fablabneuch/Pleco/Documentation/Publications/Pompage Pleco_description_annexes.pdf

# Annexes Pompes Pleco

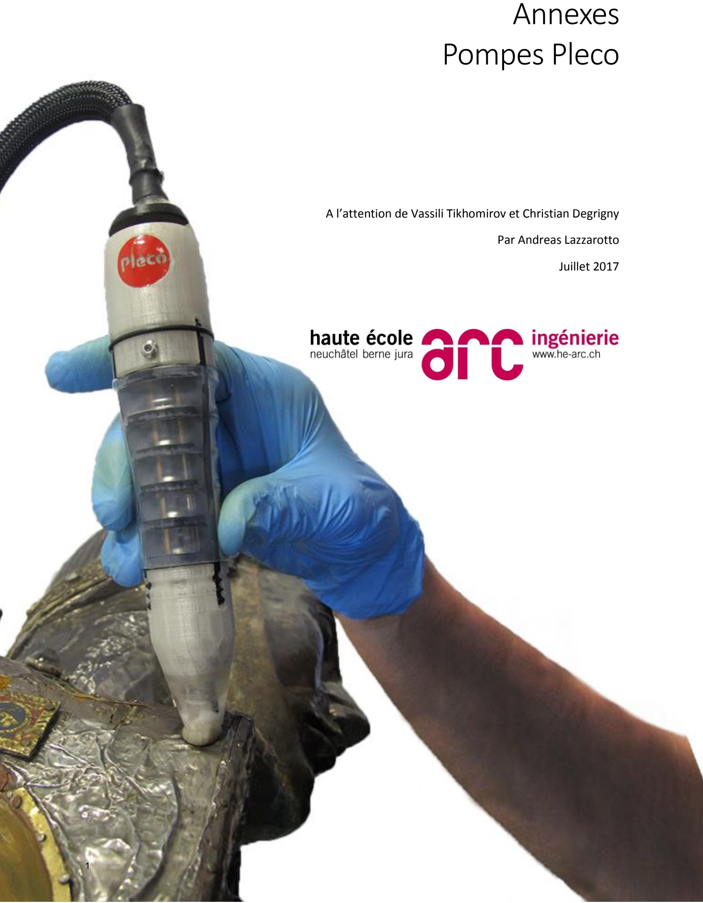
[picture p57: page 1]

A l’attention de Vassili Tikhomirov et Christian Degrigny

Par Andreas Lazzarotto

Juillet 2017

### Table des matières

A1 : Cahier des charges officiel bachelor 2016 | p3
A2 : Analyse fonctionnelle par la méthode APTE | p9
A3 : Table morphologique pompes | p14
B1.1 : Licence CERN EN | p15
B1.2 : Licence CERN traduite en FR | p19
B2 : Datasheet Arduino Leonardo | p22
B3 : Datasheet Pololu A4988 | p27

Annexe A1 : cahier des charges officiel bachelor 2016

Projet P3 & Bachelor 2015-2016 | 16IDE-TB531

# Pompes pour Pleco

Etudiant : | Lazzarotto-Pinösch Andreas | andreas.lazzarotto- pinosch@he-arc.ch
Mandant : | He-arc Conservation-Restauration
Personnes de contact : | Degrigny Christian | Christian.Degrigny@he-arc.ch
Confidentialité : | Non
Responsable du Projet : | Tikhomirov Vassili | Vassili.Tikhomirov@he-arc.ch

Description et contexte

Dans le cadre du projet P3, il m’est demandé de poursuivre mon travail commencé en cours d’anthropotechnologie de deuxième année d’ingénierie à la HE-ARC de Neuchâtel.
Le projet consiste à remplacer les pompes actuelles du pinceau électrolytique Pleco par une alternative open source / open hardware.

Objectifs
Concevoir deux pompes pour le pinceau électrolytique Pleco en tenant compte de différentes contraintes liées à l’environnement de production, à la philosophie open source et à la conception orientée vers l’utilisateur.

### 2. Conditions requises

### 2.1 Conditions relationnelles

- Une séance hebdomadaire doit être planifiée avec le responsable du projet.
- Différentes étapes doivent être validées avec le mandant, telles que la planification, le concept, la construction, les analyses. Des revues de projet doivent donc avoir lieu régulièrement avec ce dernier.
- Un journal de travail doit être tenu par le candidat au diplôme.
- Chaque semaine, un bilan succinct sur l'avancement doit être fait et les objectifs de la semaine à venir doivent être fixés. Ce document doit être transmis aux différents acteurs du projet.

### 2.2 Conditions techniques

- Le rapport de débit entre les deux pompes doit être de 1 à 10
- Moyen de comparaison entre les débits
- Faire circuler de l’air
- Avoir une fonction amorçage (bouton mettant débit max)
- Avoir une fonction pause
- Etre le plus silencieuses possible
- Supporter des pH compris entre 4 et 10.5
- Les pièces doivent pouvoir être produites dans un Fablab
- Le projet est produit dans le cadre d’une licence Open Source / Open hardware
- Ergonomie adaptée aux conservateurs restaurateurs
- Coût le plus faible possible

### 3. Travaux à exécuter

- Rapport de projet, méthodologie et conception.
- Prototypes fonctionnels

### 4. Organisation du projet P3

### 4.1 Planification

- | Début du projet P3 | 15 Février 2016
- | Liste des tâches et planification initiale à remettre | Selon professeur
- | Présentation orale et rendu de l’auto-évaluation | 13 mai 2016. Semaine 19 la date
| | sera précisée ultérieurement :

### 4.2 Présentation et expertise

- A la fin du projet P3, une présentation de 10 minutes maximum devra être faite devant le collège de professeurs. Celle-ci sera suivie de 5 minutes de questions du groupe de
| professeur(e)s.
- Chaque étudiant remettra sa grille d’auto-évaluation.

### 4.3 Annexes

- Descriptif du module Projet P3 : ING-DM3580-14

### 5. Organisation du projet Bachelor

### 5.1 Planification

- | Début du projet Bachelor | 23 mai 2016
- | Travail, rapport à remettre | 15 Juillet, au plus tard à 16h30
- Poster
- Présentation orale du projet
| | pour l'expertise du travail de diplôme
| | Semaine du 22 au 26 août, la date
| | sera précisée ultérieurement
- | Expertise du travail de Bachelor | Semaine 22 au 26 août, la date sera
| | précisée ultérieurement

### 5.2 Présentation et expertise

- L'étude et le rapport de Bachelor doivent être remis en trois exemplaires papier et un
| exemplaire sur support informatique.
- Une affiche de présentation du projet Bachelor au format A4 doit être réalisée avec approbation
| du mandant.
- Lors de l’expertise du travail de Bachelor,
- Une présentation orale de 15 minutes devra être faite devant le collège de professeurs
| garant de l’équité de jugement entre les TB.
- Une note de présentation est attribuée par le collège de professeurs.
- La soutenance se déroule ensuite avec le professeur responsable, l’expert et le
| mandant s’il le souhaite.
- A la suite de la soutenance, 3 notes sont attribuées : sur le déroulement du projet, le rapport et l’expertise. Si l’écart entre les notes du professeur et de l’expert est supérieur à 1 de manière irréconciliable, le TB fera l’objet d’une nouvelle expertise avec un autre expert et autre professeur de l’orientation.
- La note d’expertise est la moyenne pondérée des notes de présentation et de
| soutenance.

### 5.3 Annexes

- Description du module Travail de Bachelor : ING-DM3985-14
- Feuille d’enregistrement du travail de Bachelor ING-FOR3-MOD001
- Contrat Ecole – Entreprise pour projet d’étudiant ING-FOR3-MOD002
- Contrat de propriété intellectuelle et confidentialité ING-FOR3-MOD004
- Rédaction de l’affiche du travail de Bachelor : ING-FOR3-MOD005

### 6. Signatures

Neuchâtel, le 26 février 2016

L’étudiant : | Le responsable du travail de diplôme :
Lazzarotto-Pinösch Andreas | Tikhomirov Vassili
Le mandant : | La responsable de filière :
Degrigny Christian | Briquez Valérie

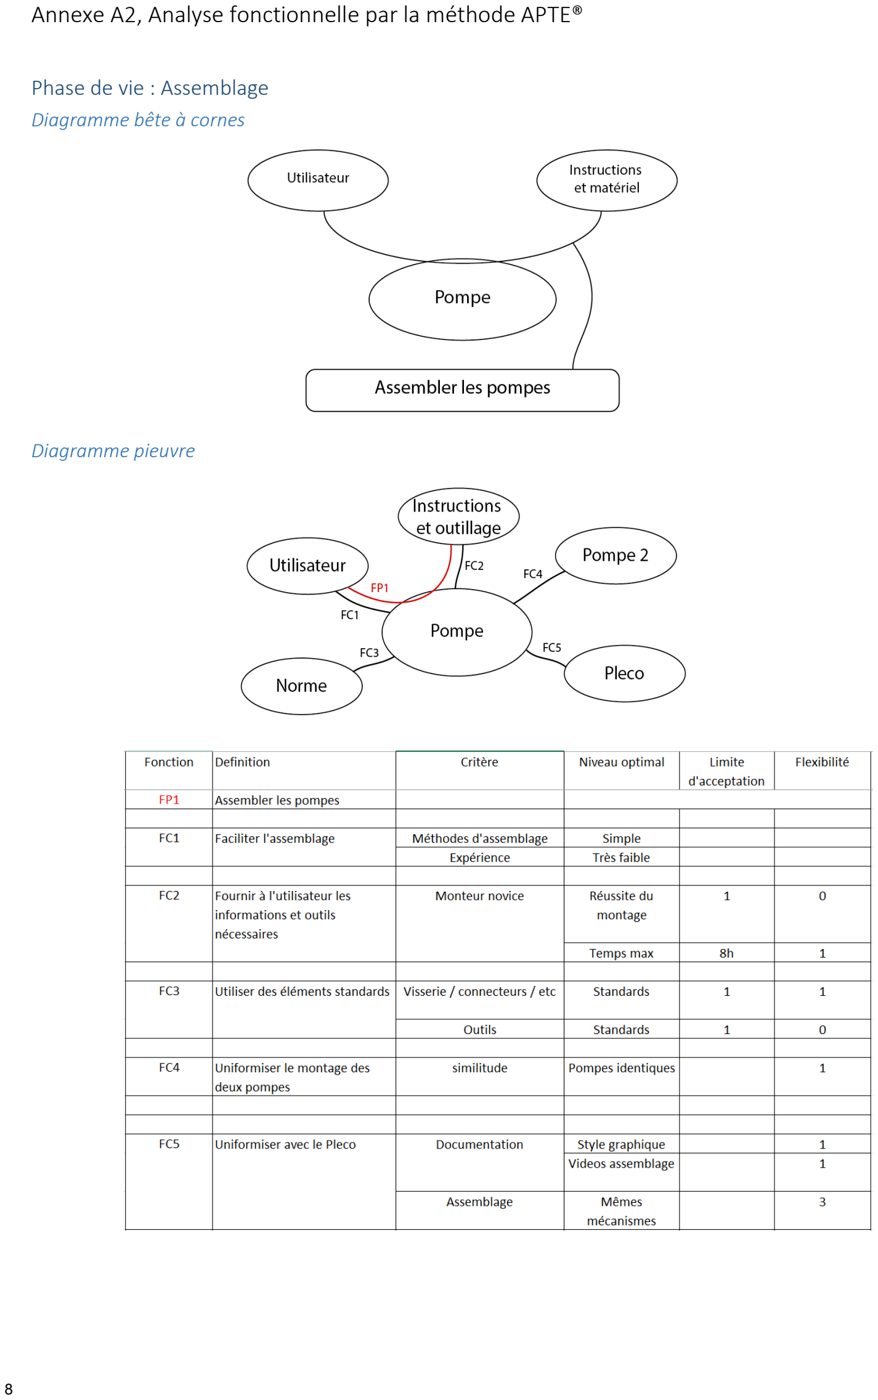
[picture p58: page 9]

### Annexe A2, Analyse fonctionnelle par la méthode APTE®

Phase de vie : Assemblage
Diagramme bête à cornes

Diagramme pieuvre

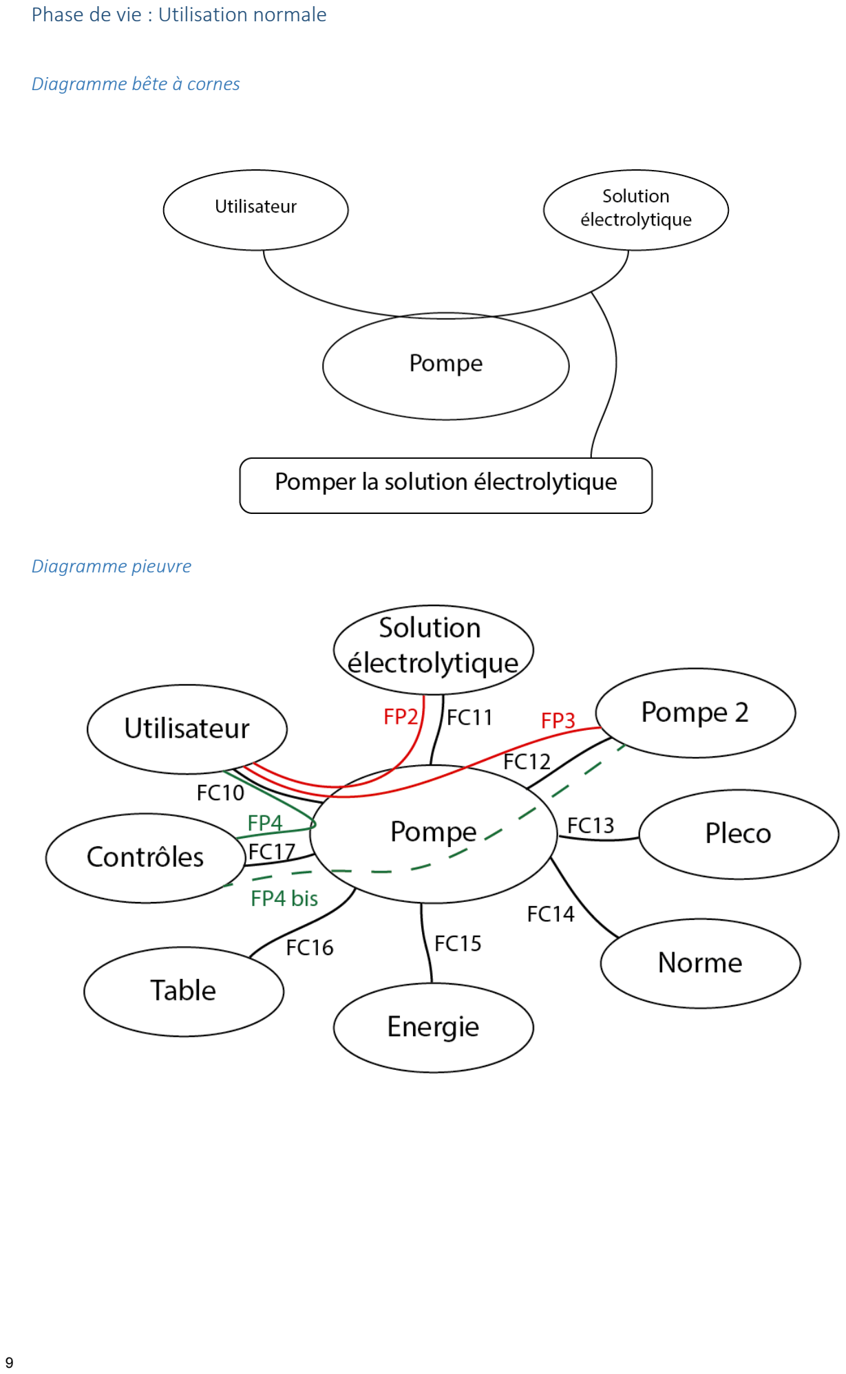
[picture p59: page 10]

Phase de vie : Utilisation normale

Diagramme bête à cornes

Diagramme pieuvre

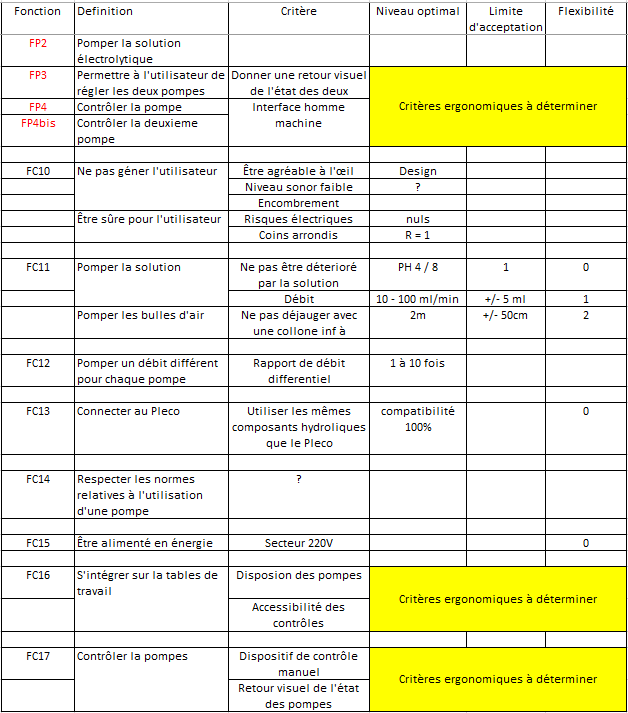
[picture p60: figure]
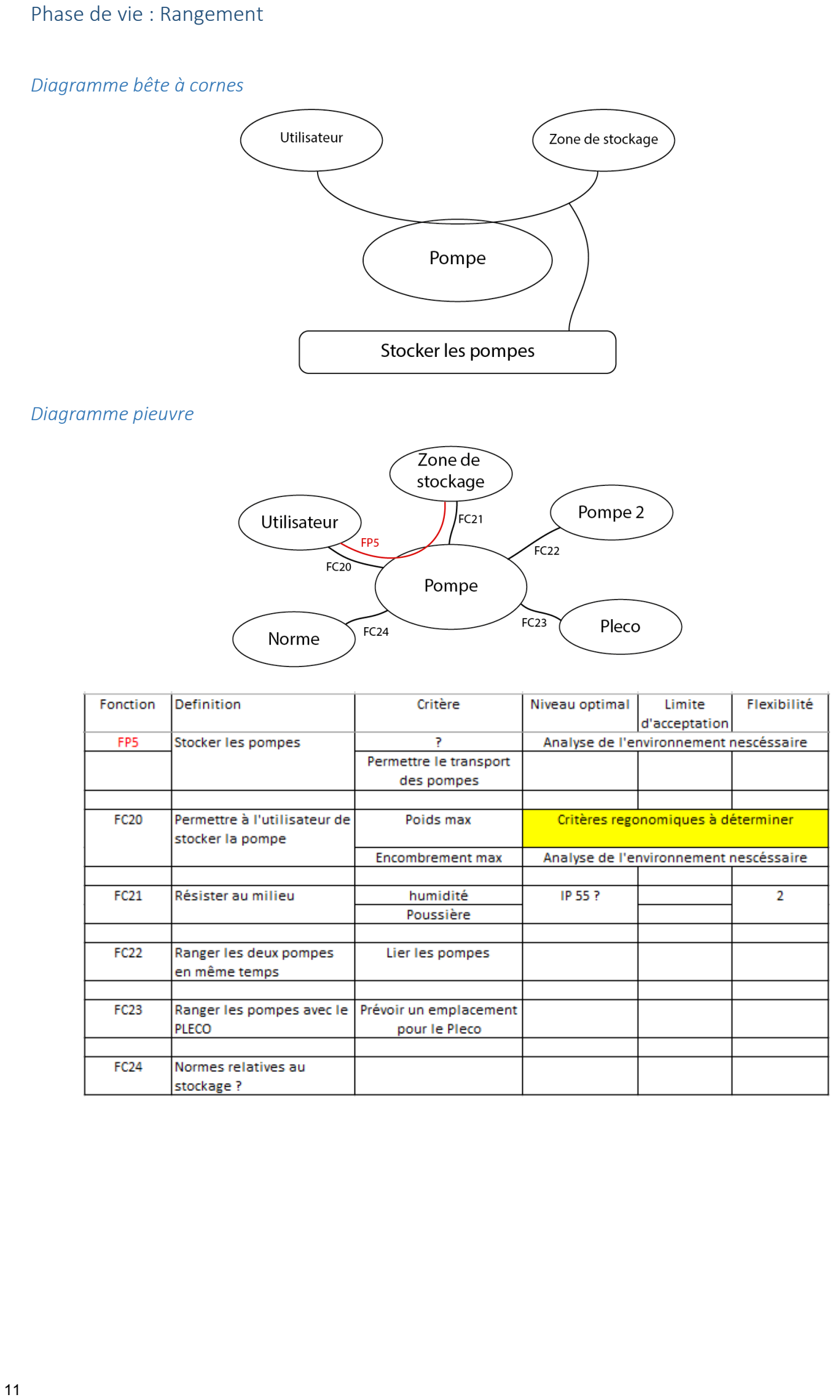
[picture p61: page 12]

Phase de vie : Rangement

Diagramme bête à cornes

Diagramme pieuvre

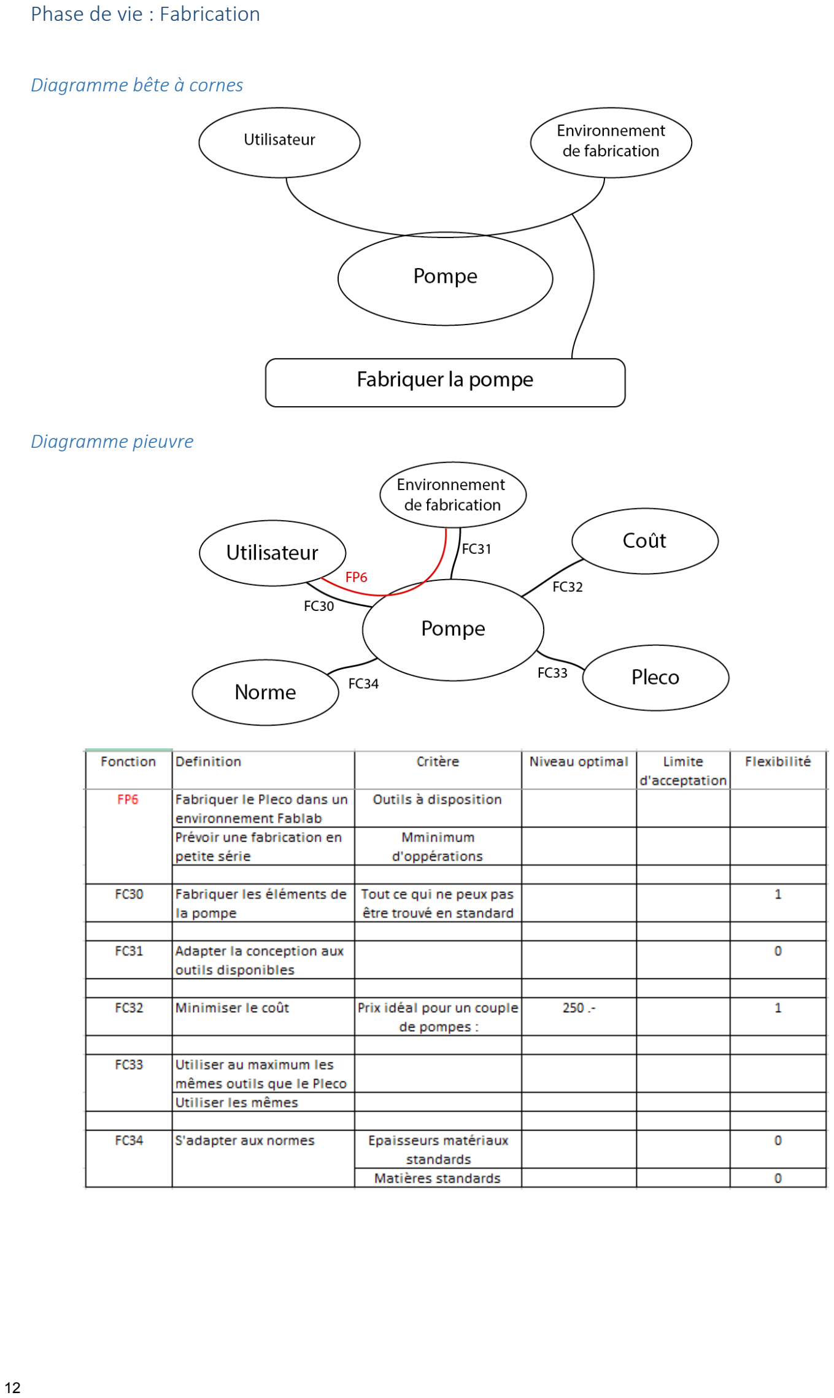
[picture p62: page 13]

Phase de vie : Fabrication

Diagramme bête à cornes

Diagramme pieuvre

Type rotative axiale rotative centrifuge à pistons pompe à palettes peristaltique à engrenages à membranes

illustration

principe physique Hélice de bateau utilisation de la force centrifuge Meme principe qu'un moteur

Le palletes restent plaquées contre
le carter et le changement de

volume entre celle-ci créent une

dépression

On comprime un tube souble

locallement pour pousser le fluide

qu'il contient

Le liquide passe a l'extérieur des

roues en étant prisonier entre les

dentures

un mouvement d'allé retour d'une
membrane dans une chambre,

assosié à des valve anti-retour met
le fluide en mouvement

Stabilitée du débit Débit constant Débit constant débit pulsé Débit constant pulsé constant pulsé

Résistance chimique Tous les éléments en contacts

doivent résister

Tous les éléments en contacts

doivent résister

Tous les éléments en contacts

doivent résister

Tous les éléments en contacts

doivent résister

Seul le tuyau est en contact avec le

fluide

Tous les éléments en contacts

doivent résister

possibilité d'utiliser des

membranes résistantes

chimiquement ( PTFE / AL / etc)

Type d'étanchéitée étanchéité par garniture sur un

arbre

étanchéité par garniture sur un

## arbre ajustement piston/carter fermeture de carter / ajustement

## hub/ pallettes/carter Pas d''étanchéitée fermeture de carter / ajustement

carter / engrenage membrane / fermeture de carter

Précision de la fabrication Critique tolérante Critique Critique Très tolérante Critique Tolérante

Fabrication dans un Fablab Dificille Difficile Très difficile Difficile Facile Difficile Moyennement dificile

## Annexe A3 : Table morphologique pompes

Annexe B1.1 Licence CERN EN

CERN Open Hardware Licence v1.2

Preamble

Through this CERN Open Hardware Licence ("CERN OHL") version 1.2, CERN wishes to provide a tool to foster collaboration and sharing among hardware designers. The CERN OHL is copyright CERN. Anyone is welcome to use the CERN OHL, in unmodified form only, for the distribution of their own Open Hardware designs. Any other right is reserved. Release of hardware designs under the CERN OHL does not constitute an endorsement of the licensor or its designs nor does it imply any involvement by CERN in the development of such designs.

1. Definitions

In this Licence, the following terms have the following meanings:

“Licence” means this CERN OHL.

“Documentation” means schematic diagrams, designs, circuit or circuit board layouts, mechanical drawings, flow charts and descriptive text, and other explanatory material that is explicitly stated as being made available under the conditions of this Licence. The Documentation may be in any medium, including but not limited to computer files and representations on paper, film, or any other media.

“Documentation Location” means a location where the Licensor has placed Documentation, and which he believes will be publicly accessible for at least three years from the first communication to the public or distribution of Documentation.

“Product” means either an entire, or any part of a, device built using the Documentation or the modified Documentation.

“Licensee” means any natural or legal person exercising rights under this Licence.

“Licensor” means any natural or legal person that creates or modifies Documentation and subsequently communicates to the public and/ or distributes the resulting Documentation under the terms and conditions of this Licence.

A Licensee may at the same time be a Licensor, and vice versa.

Use of the masculine gender includes the feminine and neuter genders and is employed solely to facilitate reading.

2. Applicability
2.1. This Licence governs the use, copying, modification, communication to the public and distribution of the Documentation, and the manufacture and distribution of Products. By exercising any right granted under this Licence, the Licensee irrevocably accepts these terms and conditions.
2.2. This Licence is granted by the Licensor directly to the Licensee, and shall apply worldwide and without limitation in time. The Licensee may assign his licence rights or grant sub-licences.
2.3. This Licence does not extend to software, firmware, or code loaded into programmable devices which may be used in conjunction with the Documentation, the modified Documentation or with Products, unless such software, firmware, or code is explicitly expressed to be subject to this Licence. The use of such software, firmware, or code is otherwise subject to the applicable licence terms and conditions.
3. Copying, modification, communication to the public and distribution of the Documentation
3.1. The Licensee shall keep intact all copyright and trademarks notices, all notices referring to Documentation Location, and all notices that refer to this Licence and to the disclaimer of warranties that are included in the Documentation. He shall include a copy thereof in every copy of the Documentation or, as the case may be, modified Documentation, that he communicates to the public or distributes.
3.2. The Licensee may copy, communicate to the public and distribute verbatim copies of the Documentation, in any medium, subject to the requirements specified in section 3.1.
3.3. The Licensee may modify the Documentation or any portion thereof provided that upon modification of the Documentation, the Licensee shall make the modified Documentation available from a Documentation Location such that it can be easily located by an original Licensor once the Licensee communicates to the public or distributes the modified Documentation under section 3.4, and, where required by section 4.1, by a recipient of a Product. However, the Licensor shall not assert his rights under the foregoing proviso unless or until a Product is distributed.
3.4. The Licensee may communicate to the public and distribute the modified Documentation (thereby in addition to being a Licensee also becoming a Licensor), always provided that he shall:
a) comply with section 3.1;
b) cause the modified Documentation to carry prominent notices stating that the Licensee has modified the Documentation, with the date and description of the modifications;
c) cause the modified Documentation to carry a new Documentation

Location notice if the original Documentation provided for one;

d) make available the modified Documentation at the same level of abstraction as that of the Documentation, in the preferred format for making modifications to it (e.g. the native format of the CAD tool as applicable), and in the event that format is proprietary, in a format viewable with a tool licensed under an OSI-approved license if the proprietary tool can create it; and
e) license the modified Documentation under the terms and conditions of this Licence or, where applicable, a later version of this Licence as may be issued by CERN.
3.5. The Licence includes a non-exclusive licence to those patents or registered designs that are held by, under the control of, or sub-licensable by the Licensor, to the extent necessary to make use of the rights granted under this Licence. The scope of this section 3.5 shall be strictly limited to the parts of the Documentation or modified Documentation created by the Licensor.
4. Manufacture and distribution of Products
4.1. The Licensee may manufacture or distribute Products always provided that, where such manufacture or distribution requires a licence under this Licence the Licensee provides to each recipient of such Products an easy means of accessing a copy of the Documentation or modified Documentation, as applicable, as set out in section 3.
4.2. The Licensee is invited to inform any Licensor who has indicated his wish to receive this information about the type, quantity and dates of production of Products the Licensee has (had) manufactured
5. Warranty and liability
5.1. DISCLAIMER – The Documentation and any modified Documentation are provided "as is" and any express or implied warranties, including, but not limited to, implied warranties of merchantability, of satisfactory quality, non-infringement of third party rights, and fitness for a particular purpose or use are disclaimed in respect of the Documentation, the modified Documentation or any Product. The Licensor makes no representation that the Documentation, modified Documentation, or any Product, does or will not infringe any patent, copyright, trade secret or other proprietary right. The entire risk as to the use, quality, and performance of a Product shall be with the Licensee and not the Licensor. This disclaimer of warranty is an essential part of this Licence and a condition for the grant of any rights granted under this Licence. The Licensee warrants that it does not act in a consumer capacity.
5.2. LIMITATION OF LIABILITY – The Licensor shall have no liability for direct, indirect, special, incidental, consequential, exemplary, punitive or other damages of any character including, without limitation, procurement of substitute goods or services, loss of use, data or profits, or business interruption, however caused and on any theory of contract, warranty, tort (including negligence), product liability or otherwise, arising in any way in relation to the Documentation, modified Documentation and/or the use, manufacture or distribution of a Product, even if advised of the possibility of such damages, and the Licensee shall hold the Licensor(s) free and harmless from any liability, costs, damages, fees and expenses, including claims by third parties, in relation to such use.
6. General
6.1. Except for the rights explicitly granted hereunder, this Licence does not imply or represent any transfer or assignment of intellectual property rights to the Licensee.
6.2. The Licensee shall not use or make reference to any of the names (including acronyms and abbreviations), images, or logos under which the Licensor is known, save in so far as required to comply with section 3. Any such permitted use or reference shall be factual and shall in no event suggest any kind of endorsement by the Licensor or its personnel of the modified Documentation or any Product, or any kind of implication by the Licensor or its personnel in the preparation of the modified Documentation or Product.
6.3. CERN may publish updated versions of this Licence which retain the same general provisions as this version, but differ in detail so far this is required and reasonable. New versions will be published with a unique version number.
6.4. This Licence shall terminate with immediate effect, upon written notice and without involvement of a court if the Licensee fails to comply with any of its terms and conditions, or if the Licensee initiates legal action against Licensor in relation to this Licence. Section 5 shall continue to apply.

Annexe B1.2 Licence CERN traduite en FR

Licence CERN Matériel Ouvert v1.2

PRÉAMBULE
Au travers cette Licence CERN Matériel Ouvert ("CERN OHL") en version 1.2, le CERN espère fournir un outil permettant de favoriser la collaboration et le partage parmi les concepteurs de Matériels. Le CERN est détenteur des droits d'auteur sur la CERN OHL. Tout le monde est le bienvenu à utiliser la CERN OHL, uniquement dans sa forme non modifiée, pour la distribution de ses conceptions de Matériel Ouvert.
Tout autre droit est réservé. La publication de conceptions de matériel sous CERN OHL ne constitue pas une acceptation du concédant ou de ses conceptions, ni n'implique une quelconque participation du CERN dans le développement de telles conceptions.
1. DÉFINITIONS
Dans cette Licence, les termes suivants ont les significations suivantes:
"Licence" signifie cette CERN OHL.
"Documentation" signifie les diagrammes schématiques, les plans, les tracés de circuit ou de circuit imprimé, les logigrammes et tout texte descriptif, et tout autre information qui est explicitement mentionné comme étant disponible sous les conditions de cette licence. La Documentation peut exister sous n'importe quel support, incluant mais ne se limitant pas aux fichiers informatiques et aux représentations sur papier, film, ou sur tout autre support. "Emplacement de la Documentation" signifie un emplacement où le Concédant a placé la Documentation, et qui sera, espère le Concédant, publiquement accessible au moins pour les trois années qui suivent la première communication au public, ou la première distribution, de la Documentation.
"Produit" signifie aussi bien tout ou partie d'un dispositif construit en utilisant la
Documentation ou la Documentation Modifiée.
"Concessionnaire" signifie toute personne physique ou morale qui exerce des droits couverts par cette Licence.
"Concédant" signifie toute personne physique ou morale qui créée ou modifie la Documentation et qui subséquemment communique au public et/ou distribue la Documentation qui en résulte sous les termes et conditions de cette Licence.
Un Concédant peut être à la fois un Concessionnaire, et vice versa.
L'utilisation du genre masculin inclus le genre féminin et le genre neutre, et est employé uniquement pour faciliter la lecture.
2. APPLICABILITÉ
2.1 Cette licence régit l'utilisation, la reproduction, la modification, la communication au public et la distribution de la Documentation, ainsi que la fabrication et distribution des Produits. Par l'exercice de tout droit accordé en vertu de cette Licence, le Concessionnaire accepte de façon irrévocable ces termes et conditions.
2.2 Cette Licence est accordée par le Concédant directement au
Concessionnaire, et elle s'applique dans le monde entier et sans limitation dans le temps. Le Concessionnaire peut céder ses droits de licence ou concéder des sous-licences.
2.3 Cette licence ne s'étend pas aux logiciels, aux micrologiciels, ou aux codes chargés dans des dispositifs programmables qui peuvent être utilisés en conjonction avec la Documentation, la Documentation modifiée ou avec les Produits, à moins qu'un tel logiciel, micrologiciel, ou code ne soit explicitement exprimé comme étant soumis à cette Licence. Autrement, l'utilisation d'un tel logiciel, micrologiciel, ou code est, soumis aux termes et conditions de la licence applicable.
3. REPRODUCTION, MODIFICATION, COMMUNICATION AU PUBLIC
ET DISTRIBUTION DE LA DOCUMENTATION.
3.1 Le Concessionnaire doit conserver intacts tous les droits d'auteurs et les licences de marques, toutes les notices se référant à l'Emplacement de laDocumentation, et toutes les notices qui se réfèrent à cette Licence et à la déclaration d'absence de garanties qui sont inclus dans la Documentation.

3.2 Le Concessionnaire peut copier, communiquer au public et distribuer des copies verbatim de la Documentation, sur n'importe quel support, selon les exigences spécifiées dans la section 3.1.
3.3 Le Concessionnaire peut modifier la documentation ou toute portion de celle-ci à condition que lors de la modification de la documentation, le Concessionnaire rende la Documentation Modifiée disponible depuis un Emplacement de la Documentation de telle sorte à ce qu'elle soit facilement localisée par un Concédant initial dès que le concessionnaire communique au public ou distribue la Documentation Modifiée en vertu de la section 3.4, et, comme stipulé par la section 4.1, par un destinataire d'un Produit. Toutefois, le Concédant ne pourra faire valoir ses droits en vertu de la clause restrictive précédente, à moins que ou jusqu'à ce que, un Produit soit distribué.
3.4 Le Concessionnaire peut communiquer au public et distribuer la Documentation Modifiée (de ce fait en plus d'être un Concessionnaire devenant également un Concédant ), à condition qu'il doive toujours :
a) être conforme avec la section 3.1;
b) faire de telle sorte à ce que la Documentation Modifiée contienne de
façon bien en évidence des notices stipulant que le Concessionnaire a modifié la Documentation, avec la date et la description des modifications;
c) faire de telle sorte à ce que la Documentation Modifiée contienne un nouvel Emplacement de Documentation lorsque la Documentation initiale en prévit un;
d) rendre disponible la Documentation Modifiée dans un même niveau d'abstraction que celui de la Documentation, dans une forme préférée pour faire des modifications sur celle-ci (càd: le format natif d'un outil de CAO qui s'applique), et dans le cas où ce format est propriétaire, dans un format consultable avec un outil régit par des termes et conditions sous une licence approuvée par l'OSI si l'outil propriétaire peut le créer; et e) placer la documentation Modifiée sous les termes et conditions de cette Licence ou, lorsque cela s'applique, une version postérieure de cette Licence susceptible d'être émise par le CERN.
3.5. La Licence inclus une licence non-exclusive pour ces brevets ou ces marques déposées qui sont détenus par, sous le contrôle de, ou souslicenciable par le Concédant, dans la mesure nécessaire pour faire usage des droits accordés en vertu de cette Licence. Le champ de cette section
3.5 doit être strictement limité aux parties de le Documentation ou de la
Documentation Modifiée créée par le Concédant.
4. FABRICATION ET DISTRIBUTION DES PRODUITS
4.1. Le Concessionnaire peut fabriquer ou distribuer les Produits à la condition permanente que, lorsqu'une telle fabrication ou distribution requiert une licence sous cette Licence, le Concessionnaire fournisse à chaque destinataire de telle produits un moyen facile pour accéder à une copie de la Documentation ou de la Documentation Modifiée, comme cela s'applique, comme établit en section 3.
4.2. Le Concessionnaire est invité à informer tout Concédant qui a indiqué qu'il souhaite recevoir cette information à propos du type, de la quantité et des dates de production des produits que le Concessionnaire a (avait) fabriqués.
5. GARANTIE ET RESPONSABILITÉ
5.1 RENONCIATION - La Documentation et la Documentation
Modifiée sont fournies "en l'état" et toute garantie exprimée ou tacite, incluant, mais ne se limitant pas à, les garanties tacites de commercialisation (en terme de qualité, état, qualité, existence), de qualité satisfaisante, non-violation de droits de tiers, et d'adéquation à un objectif particulier ou à un usage, est exclue en ce qui concerne la Documentation, la Documentation modifiée ou tout Produit. Le Concédant ne fait aucune déclaration qui stipulerait que la Documentation, la Documentation Modifiée, ou tout Produit, est ou sera en violation avec un brevet, un droit d'auteur, un secret d'état ou une autre droit de propriété. La totalité du risque quant à l'utilisation, la qualité, et la performance d'un Produit, est assumé par le Concessionnaire et pas par le Concédant. Cette renonciation de garantie est une partie essentielle de cette Licence et une condition pour l'octroie de tous droits en vertu de cette Licence. Le Concessionnaire garantie qu'il n'agit pas en qualité de consommateur.

5.2 LIMITE DE RESPONSABILITÉ - Le Concédant ne peut aucunement être tenu responsable d'aucune façon pour des dommages de tout type directs, indirects, spéciaux, consécutifs, exemplaires, punitifs ou autres, incluant, mais pas limité aux, achats de marchandises de remplacement ou de services, perte d'utilisation, de données ou de profits, ou interruption d'activités, même provoqués et fondés sur une quelconque théorie de contrat, de garantie, de délis (incluant la négligence), de responsabilité liée au produit ou quelque soit d'autre, survenant de n'importe quelle façon en relation avec la Documentation, la Documentation Modifiée et/ou l'utilisation, la fabrication ou la distribution d'un produit, même s'il est avisé de l'éventualité de tels dommages, et il est de la responsabilité du Concessionnaire de tenir le(s) Concédant(s) libre(s) et exonéré(s) toute responsabilité, coûts, dommages, frais et dépenses, y compris les réclamations de tiers, en relation avec à une telle utilisation.
6. GENERAL
6.1 À l'exception des droits explicitement accordés aux présentes, cette licence ni ne signifie ni ne représente un quelconque transfert ou une quelconque cession des droits de propriété intellectuelle au Concessionnaire.
6.2. Le Concessionnaire ne doit pas utiliser ou faire référence à de quelconques noms (incluant les acronymes et les abréviations), images, ou logos en vertu desquels le Concédant est connu, sauf dans la mesure où cela est requis pour se conformer avec la section 3. Une telle utilisation autorisée ou référence doit être factuelle et ne doit en aucun cas suggérer une quelconque sorte d'approbation, par le Concédant ou son personnel, de la Documentation Modifiée ou de tout Produit, ou une quelconque implication par le Concédant ou son personnel, dans la préparation de la Documentation Modifiée ou du Produit.
6.3. Le CERN peut publier des versions mises à jour de cette Licence qui conservent les mêmes dispositions générales que cette version, mais diffèrent dans les détails dans la limite du nécessaire et du raisonnable. Les nouvelles versions seront publiées avec un numéro de version unique.
6.4. Cette Licence prend fin avec effet immédiat, moyennant un préavis écrit et sans intervention d'un tribunal si le Concessionnaire échoue à se mettre en conformité avec un quelconque de ses termes et conditions, ou si le Concessionnaire initie une action en justice contre le Concédant enrelation avec cette Licence. La section 5 doit continuer à s'appliquer.

## Annexe B1 : Datasheet Arduino Leonardo

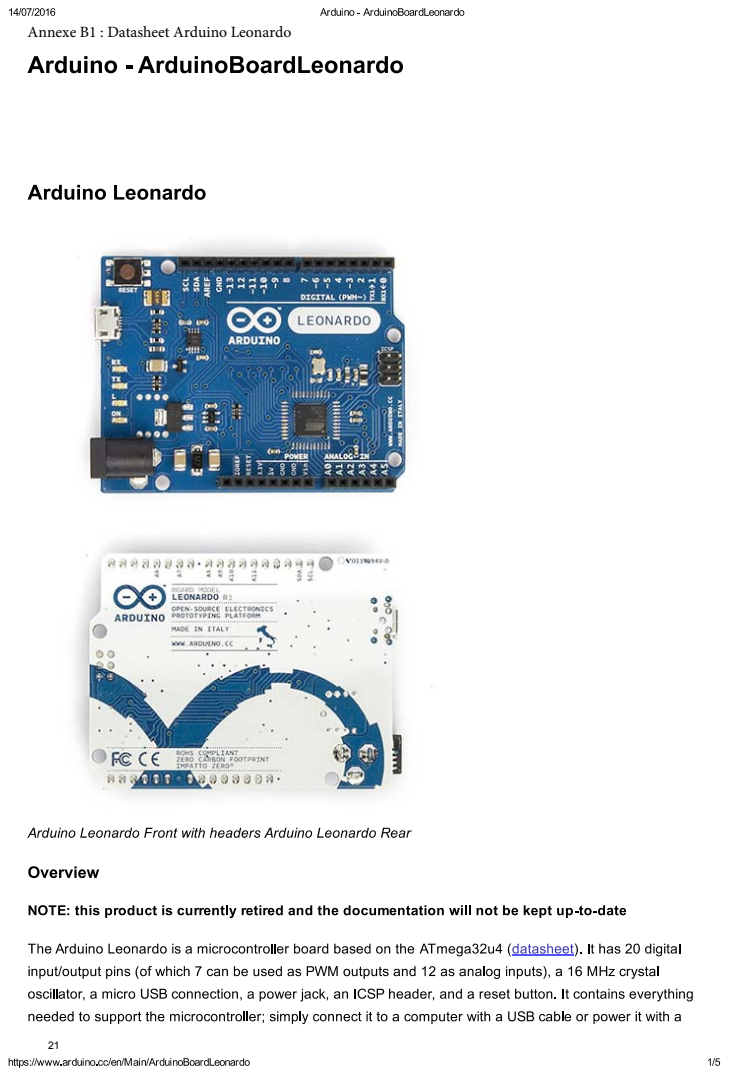
[picture p63: page 22]

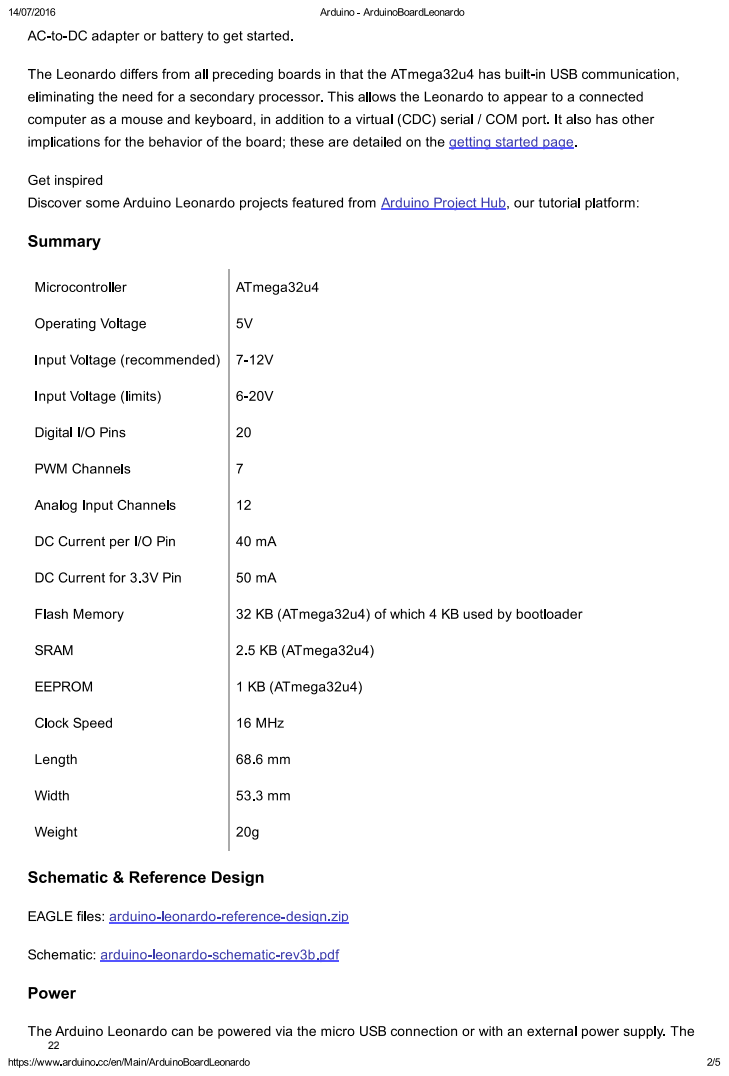
[picture p64: page 23]

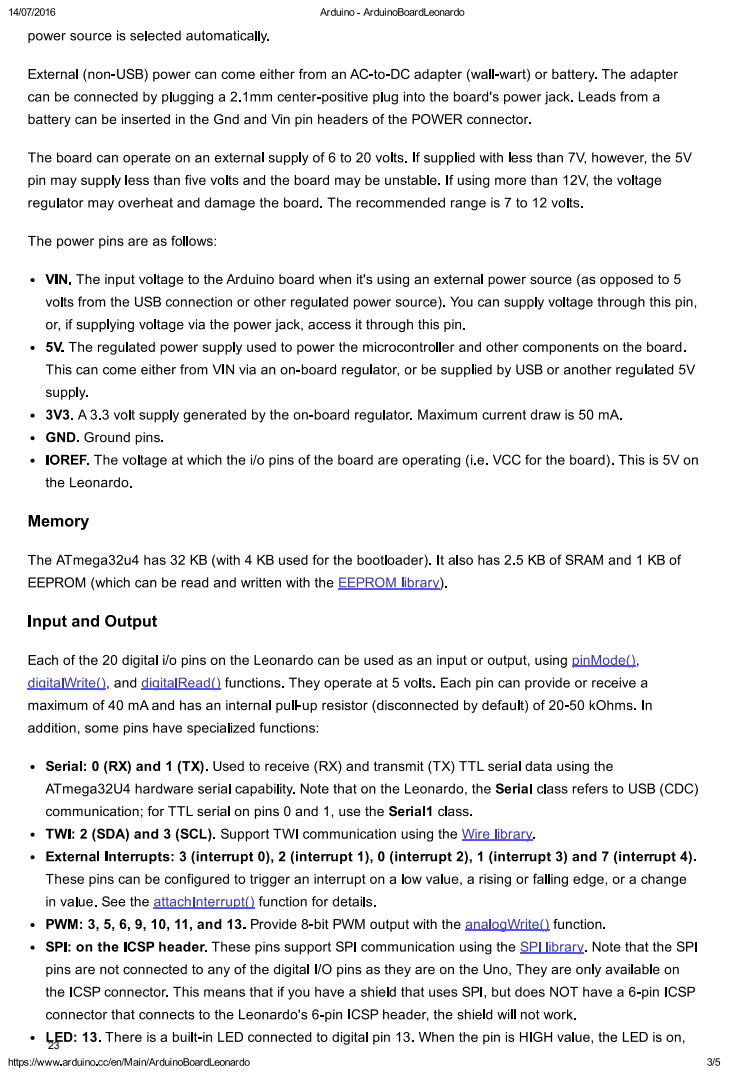
[picture p65: page 24]

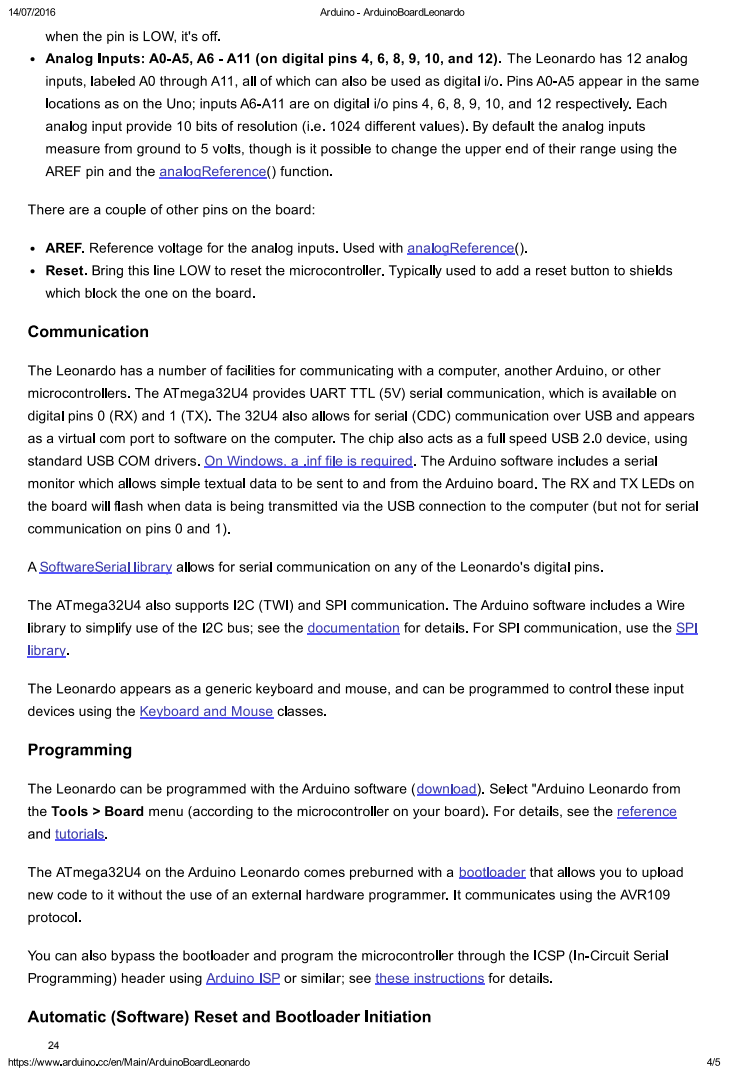
[picture p66: page 25]

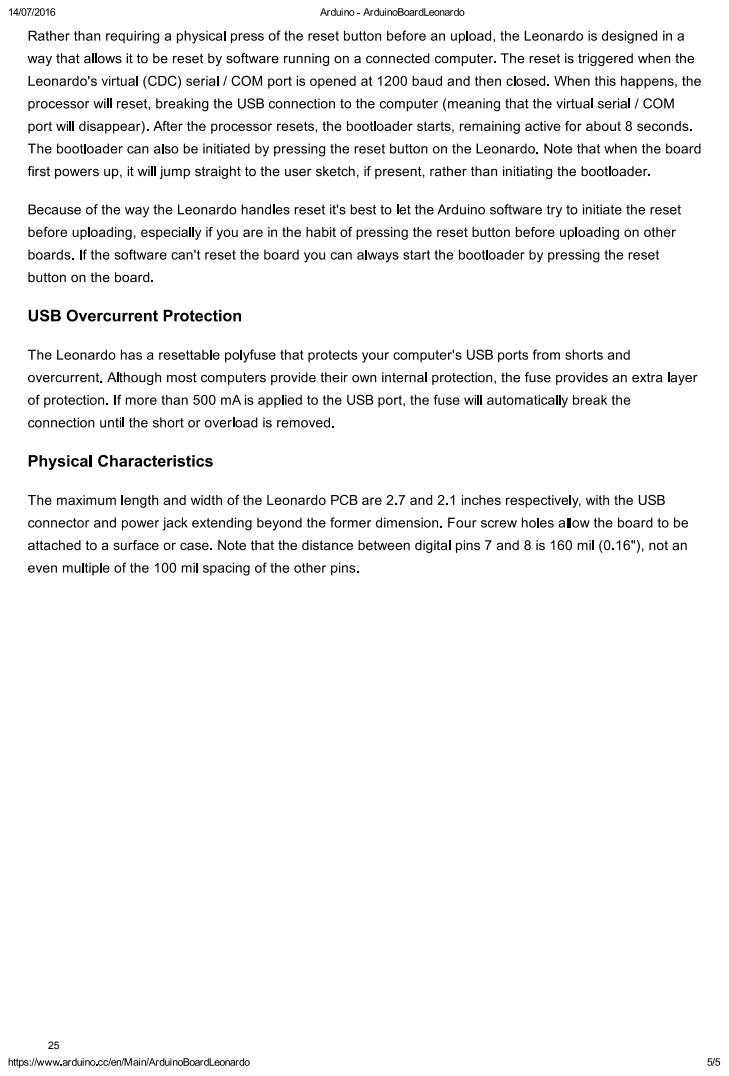
[picture p67: page 26]

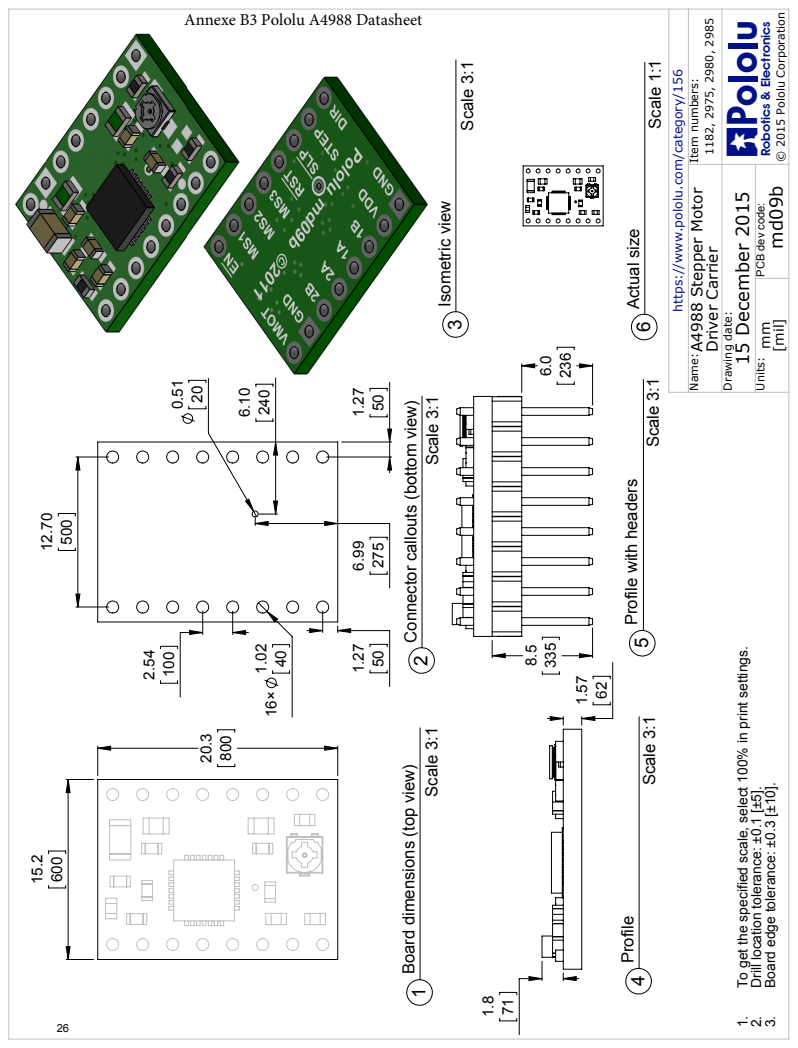
[picture p68: page 27]
Scale 3:1; Isometric view 3; Profile 4 6 Scale 1:1; Actual size; Name:; Drawing date:; Units: mm; [mil]; Item numbers:; 15 December 2015; 1182, 2975, 2980, 2985 A4988 Stepper Motor; Driver Carrier; Robotics & Electronics

© 2015 Pololu CorporationAnnexe B3 Pololu A4988 Datasheet

https://www.pololu.com/category/156

PCB dev code:

Connector callouts (bottom view) 2

Profile with headers 5

To get the specified scale, select 100% in print settings. 1.

1 Board dimensions (top view)

Drill location tolerance: ±0.1 [±5]. 2.

Board edge tolerance: ±0.3 [±10]. 3.

## Features and Benefits

- Low RDS(ON) outputs - Automatic current decay mode detection/selection - Mixed and Slow current decay modes - Synchronous rectification for low power dissipation - Internal UVLO - Crossover-current protection - 3.3 and 5 V compatible logic supply - Thermal shutdown circuitry - Short-to-ground protection - Shorted load protection - Five selectable step modes: full, ¹/2, ¹/4, ¹/8, and ¹/16

## Package:

## Description

The A4988 is a complete microstepping motor driver with built-in translator for easy operation. It is designed to operate bipolar stepper motors in full-, half-, quarter-, eighth-, and sixteenth-step modes, with an output drive capacity of up to 35 V and ±2 A. The A4988 includes a fixed off-time current regulator which has the ability to operate in Slow or Mixed

decay modes.

### The translator is the key to the easy implementation of the A4988. Simply inputting one pulse on the STEP input drives

the motor one microstep. There are no phase sequence tables, highfrequencycontrollines,or complexinterfacesto program.

### The A4988 interface is an ideal fit for applications where a

complex microprocessor is unavailable or is overburdened.

### During stepping operation, the chopping control in the A4988

automatically selects the current decay mode, Slow or Mixed.

### In Mixed decay mode, the device is set initially to a fast decay for a proportion of the fixed off-time, then to a slow decay for the remainder of the off-time. Mixed decay current control

resultsinreducedaudiblemotornoise,increasedstepaccuracy, and reduced power dissipation.

# DMOS Microstepping Driver with Translator And Overcurrent Protection

Continued on the next page…

A4988

Approximate size

28-contact QFN

### with exposed thermal pad

5 mm × 5 mm × 0.90 mm
(ET package)

## Typical Application Diagram

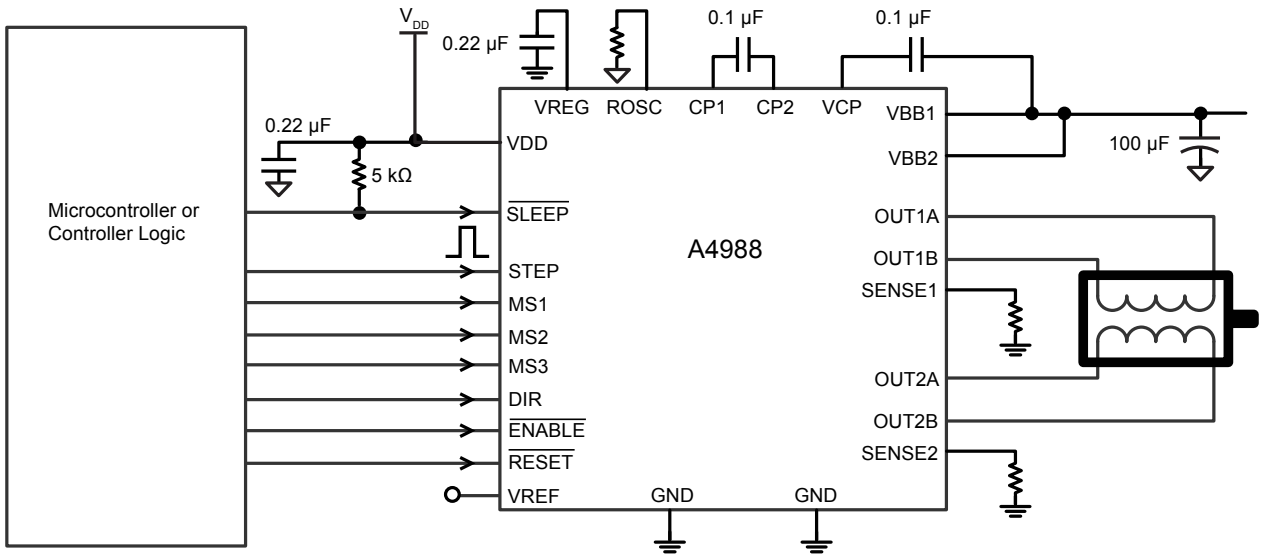
[picture p69: figure]
Microcontroller or Controller Logic; VDD; VREF; GND; RESET; ENABLE; SLEEP; DIR; STEP; VREG; VCP VBB1; ROSC; VBB2; OUT1A; OUT1B SENSE1; OUT2A; OUT2B SENSE2

4988-DS, Rev. 5

# DMOS Microstepping Driver with Translator And Overcurrent Protection A4988

Allegro MicroSystems, LLC | 2 115 Northeast Cutoff

Worcester, Massachusetts 01615-0036 U.S.A. 1.508.853.5000; www.allegromicro.com

### Internal synchronous rectification control circuitry is provided to improve power dissipation during PWM operation. Internal

circuit protection includes: thermal shutdown with hysteresis, undervoltage lockout (UVLO), and crossover-current protection. Special power-on sequencing is not required.

### TheA4988 issupplied in a surfacemount QFN package (ES), 5mm × 5 mm, with a nominal overall package height of 0.90 mm and an exposed pad for enhanced thermal dissipation. It is lead (Pb) free

(suffix –T), with 100% matte tin plated leadframes.

## Description (continued)

## Absolute Maximum Ratings

Characteristic | Symbol | Notes | Rating | Units
Load Supply Voltage | VBB | | 35 | V
Output Current | IOUT | | ±2 | A
Logic Input Voltage | VIN | | –0.3 to 5.5 | V
Logic Supply Voltage | VDD | | –0.3 to 5.5 | V
Motor Outputs Voltage | | | –2.0 to 37 | V
Sense Voltage | VSENSE | | –0.5 to 0.5 | V
Reference Voltage | VREF | | 5.5 | V
Operating Ambient Temperature | TA | Range S | –20 to 85 | ºC
Maximum Junction | TJ(max) | | 150 | ºC
Storage Temperature | Tstg | | –55 to 150 | ºC

## Selection Guide

Part Number | Package | Packing
A4988SETTR-T | 28-contact QFN with exposed thermal pad | 1500 pieces per 7-in. reel

# DMOS Microstepping Driver with Translator And Overcurrent Protection A4988

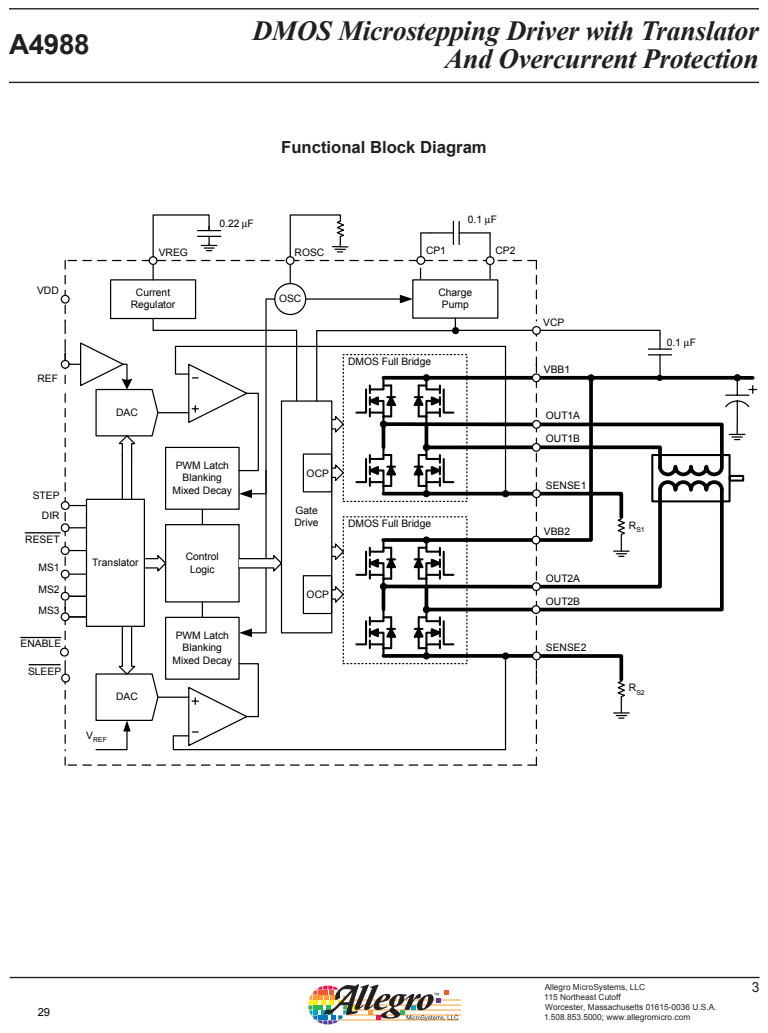
[picture p70: page 30]
Allegro MicroSystems, LLC; 3 115 Northeast Cutoff; SENSE1; SENSE2; VREG; VCP; Control Logic; DAC; VDD; PWM Latch Blanking Mixed Decay; STEP DIR; RESET; Current Regulator; Charge Pump; VBB1; OUT1A; OUT1B; VBB2; OUT2A; OUT2B; VREF; Translator; Gate; Drive; DMOS Full Bridge; OSC; ROSC; REF; ENABLE; SLEEP; OCP

Functional Block Diagram

DMOS Full Bridge

Worcester, Massachusetts 01615-0036 U.S.A.
1.508.853.5000; www.allegromicro.com

# DMOS Microstepping Driver with Translator And Overcurrent Protection A4988

Allegro MicroSystems, LLC | 4 115 Northeast Cutoff

Worcester, Massachusetts 01615-0036 U.S.A. 1.508.853.5000; www.allegromicro.com

ELECTRICAL CHARACTERISTICS¹ at TA = 25°C, VBB = 35 V (unless otherwise noted)
Characteristics | Symbol | Test Conditions | Min. | Typ.² | Max. | Units

### Output Drivers

Load Supply Voltage Range | VBB | Operating | 8 | – | 35 | V
Logic Supply Voltage Range | VDD | Operating | 3.0 | – | 5.5 | V
Output On Resistance | RDSON | Source Driver, IOUT = –1.5 A | – | 320 | 430 | mΩ
| | Sink Driver, IOUT = 1.5 A | – | 320 | 430 | mΩ
Body Diode Forward Voltage | VF | Source Diode, IF = –1.5 A | – | – | 1.2 | V
| | Sink Diode, IF = 1.5 A | – | – | 1.2 | V
Motor Supply Current | IBB | fPWM < 50 kHz | – | – | 4 | mA
| | Operating, outputs disabled | – | – | 2 | mA
Logic Supply Current | IDD | fPWM < 50 kHz | – | – | 8 | mA
| | Outputs off | – | – | 5 | mA

### Control Logic

Logic Input Voltage | VIN(1) | | VDD×0.7 | – | – | V
| VIN(0) | | – | – | VDD×0.3 | V
Logic Input Current | IIN(1) | VIN = VDD×0.7 | –20 | <1.0 | 20 | µA
| IIN(0) | VIN = VDD×0.3 | –20 | <1.0 | 20 | µA
Microstep Select | RMS1 | MS1 pin | – | 100 | – | kΩ
| RMS2 | MS2 pin | – | 50 | – | kΩ
| RMS3 | MS3 pin | – | 100 | – | kΩ
Logic Input Hysteresis | VHYS(IN) | As a % of VDD | 5 | 11 | 19 | %
Blank Time | tBLANK | | 0.7 | 1 | 1.3 | μs
Fixed Off-Time | tOFF | OSC = VDD or GND | 20 | 30 | 40 | μs
| | ROSC = 25 kΩ | 23 | 30 | 37 | μs
Reference Input Voltage Range | VREF | | 0 | – | 4 | V
Reference Input Current | IREF | | –3 | 0 | 3 | μA
Current Trip-Level Error³ | errI | VREF = 2 V, %ITripMAX = 38.27% | – | – | ±15 | %
| | VREF = 2 V, %ITripMAX = 70.71% | – | – | ±5 | %
| | VREF = 2 V, %ITripMAX = 100.00% | – | – | ±5 | %
Crossover Dead Time | tDT | | 100 | 475 | 800 | ns

### Protection

Overcurrent Protection Threshold⁴ | IOCPST | | 2.1 | – | – | A
Thermal Shutdown Temperature | TTSD | | – | 165 | – | °C
Thermal Shutdown Hysteresis | TTSDHYS | | – | 15 | – | °C
VDD Undervoltage Lockout | VDDUVLO | VDD rising | 2.7 | 2.8 | 2.9 | V
VDD Undervoltage Hysteresis | VDDUVLOHYS | | – | 90 | – | mV
1For input and output current specifications, negative current is defined as coming out of (sourcing) the specified device pin.
2Typical data are for initial design estimations only, and assume optimum manufacturing and application conditions. Performance may vary for individual units, within the specified maximum and minimum limits.
3VERR = [(VREF/8) – VSENSE] / (VREF/8).
4Overcurrent protection (OCP) is tested at TA = 25°C in a restricted range and guaranteed by characterization.
