fablabneuch/Pleco/wiki/images/1. Analyse - Outil CLAMTEC/download (1).png

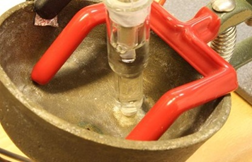
wiki/images/1. Analyse - Outil CLAMTEC/download (1).png
