fablabneuch/Pleco/wiki/images/1. Analyse - Outil CLAMTEC/download (5).png

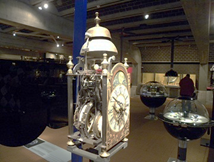
wiki/images/1. Analyse - Outil CLAMTEC/download (5).png
