fablabneuch/Pleco/wiki/images/1. Analyse - Outil CLAMTEC/download.png

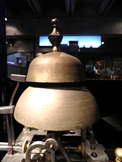
wiki/images/1. Analyse - Outil CLAMTEC/download.png
