fablabneuch/Pleco/wiki/images/4. Application en Conservation-restauration Stabilisation/download (2).jpg

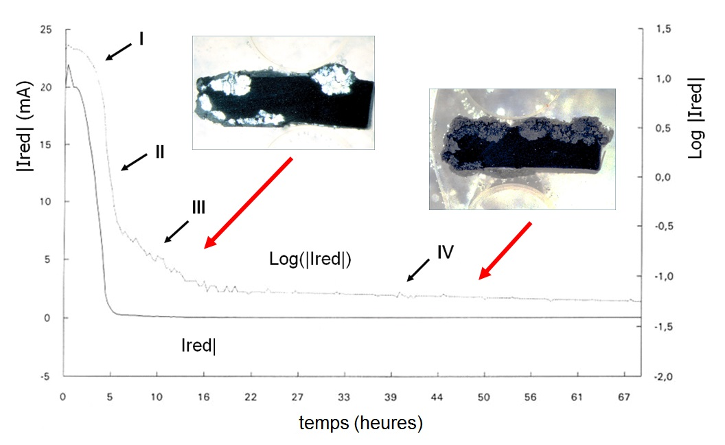
wiki/images/4. Application en Conservation-restauration Stabilisation/download (2).jpg
