fablabneuch/Pleco/wiki/images/4. Application en Conservation-restauration Stabilisation/download (5).png

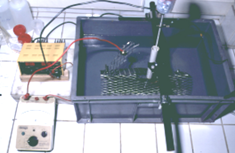
wiki/images/4. Application en Conservation-restauration Stabilisation/download (5).png
