fablabneuch/Pleco/wiki/images/4. Application en Conservation-restauration Stabilisation/download (7).png

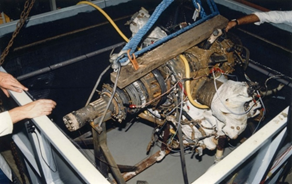
wiki/images/4. Application en Conservation-restauration Stabilisation/download (7).png
