fablabneuch/Pleco/wiki/images/4. Application en Conservation-restauration Stabilisation/download (10).png

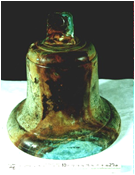
wiki/images/4. Application en Conservation-restauration Stabilisation/download (10).png
