fablabneuch/Pleco/wiki/images/4. Application en Conservation-restauration Stabilisation/download.jpg

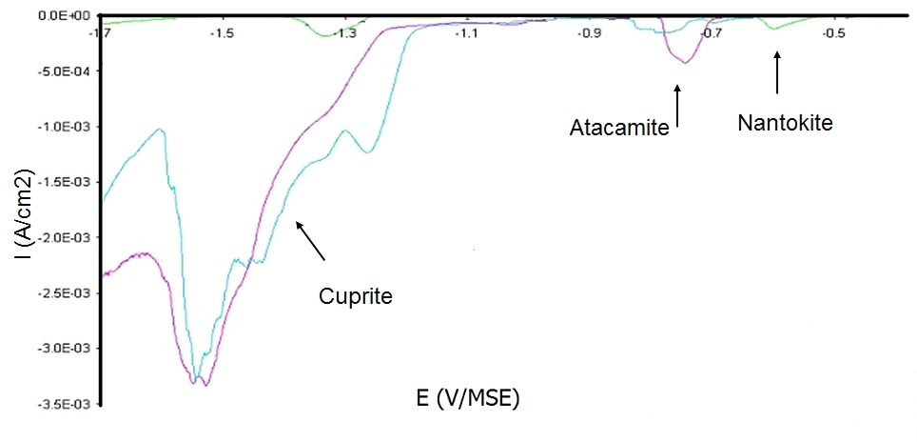
wiki/images/4. Application en Conservation-restauration Stabilisation/download.jpg
