fablabneuch/Pleco/wiki/images/4. Application en Conservation-restauration Stabilisation/download.png

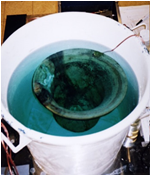
wiki/images/4. Application en Conservation-restauration Stabilisation/download.png
