fablabneuch/Pleco/wiki/images/Electrochimie - Principes de base/download (1).png

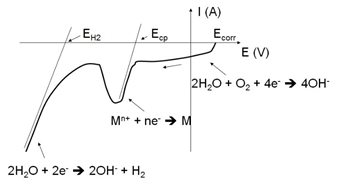
wiki/images/Electrochimie - Principes de base/download (1).png
