fablabneuch/Pleco/wiki/images/Electrochimie - Principes de base/download (2).png

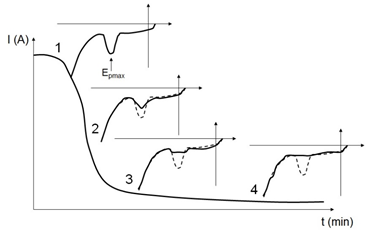
wiki/images/Electrochimie - Principes de base/download (2).png
