fablabneuch/Pleco/wiki/images/Electrochimie - Principes de base/download.png

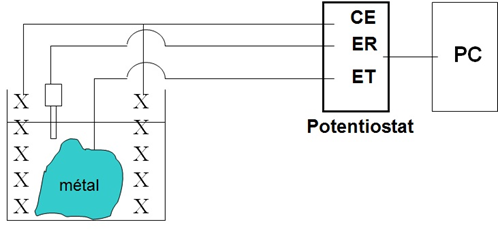
wiki/images/Electrochimie - Principes de base/download.png
