fablabneuch/Pleco/wiki/images/Fabriquer Aquérir son Pleco/IMG_5603.jpg

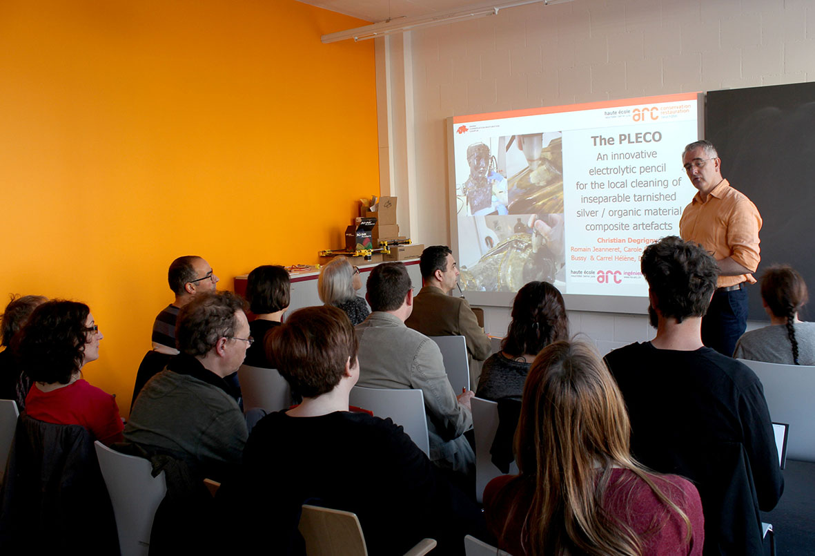
wiki/images/Fabriquer Aquérir son Pleco/IMG_5603.jpg
