fablabneuch/Pleco/wiki/images/Fabriquer Aquérir son Pleco/IMG_5620.jpg

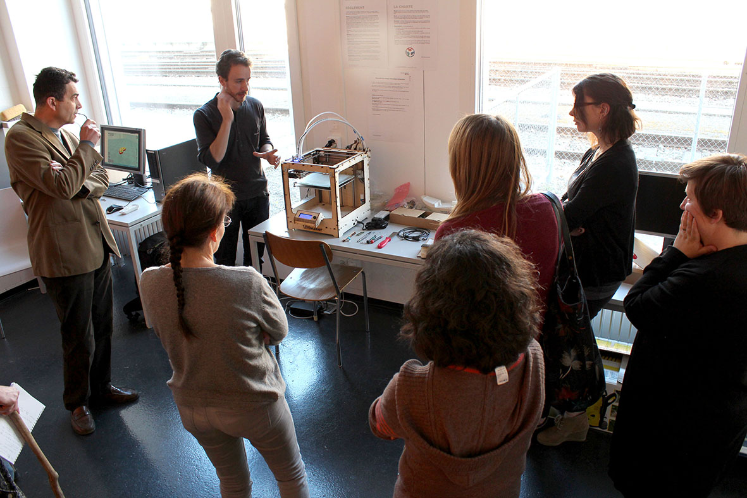
wiki/images/Fabriquer Aquérir son Pleco/IMG_5620.jpg
