fablabneuch/Pleco/wiki/images/Fabriquer Aquérir son Pleco/IMG_5629.jpg

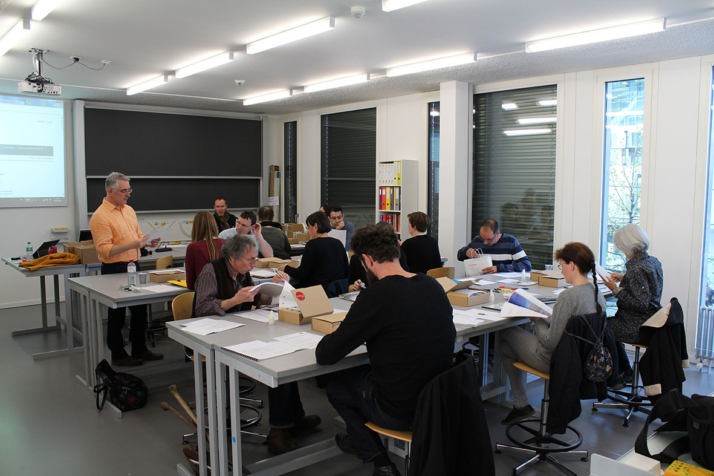
wiki/images/Fabriquer Aquérir son Pleco/IMG_5629.jpg
