fablabneuch/Pleco/wiki/images/Fabriquer Aquérir son Pleco/IMG_5639.jpg

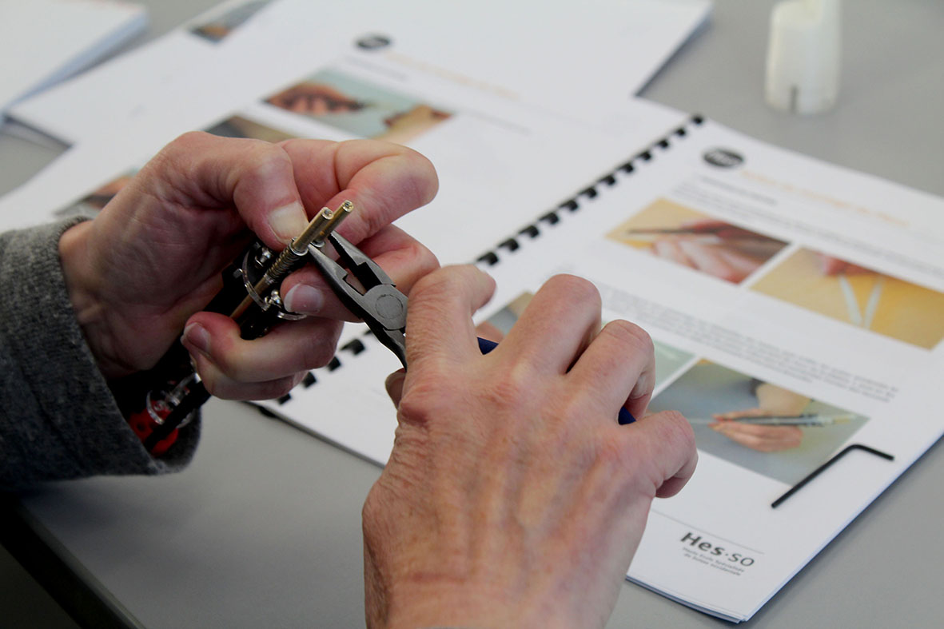
wiki/images/Fabriquer Aquérir son Pleco/IMG_5639.jpg
