fablabneuch/Pleco/wiki/images/Fabriquer Aquérir son Pleco/IMG_5660.jpg

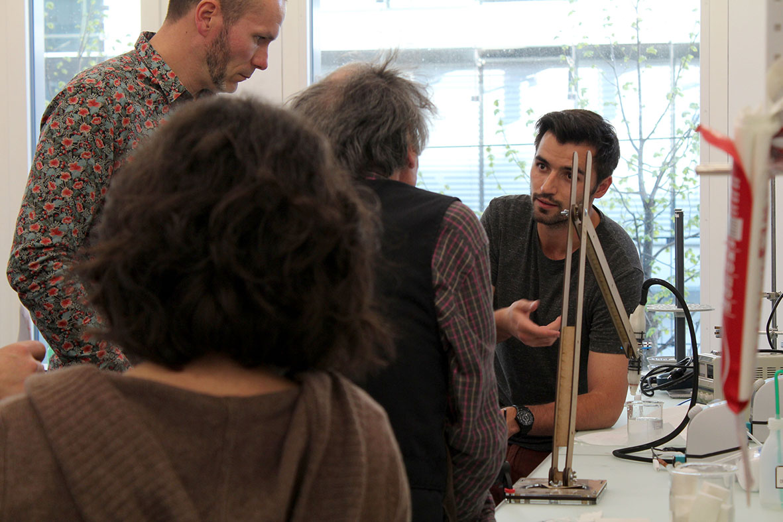
wiki/images/Fabriquer Aquérir son Pleco/IMG_5660.jpg
