fablabneuch/Pleco/wiki/images/Le Pleco The Pleco/download.png

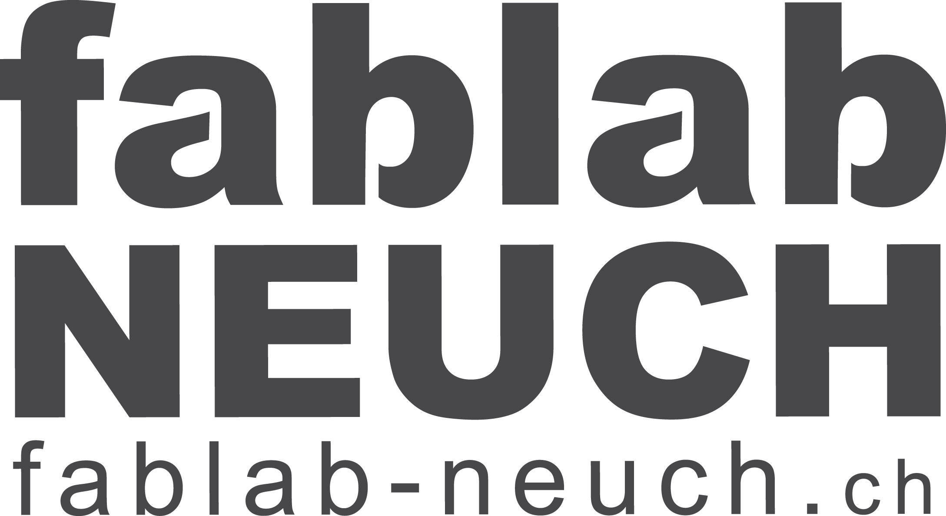
wiki/images/Le Pleco The Pleco/download.png
