fablabneuch/Pleco/wiki/images/Le Pleco The Pleco/IMG_0143b.jpg

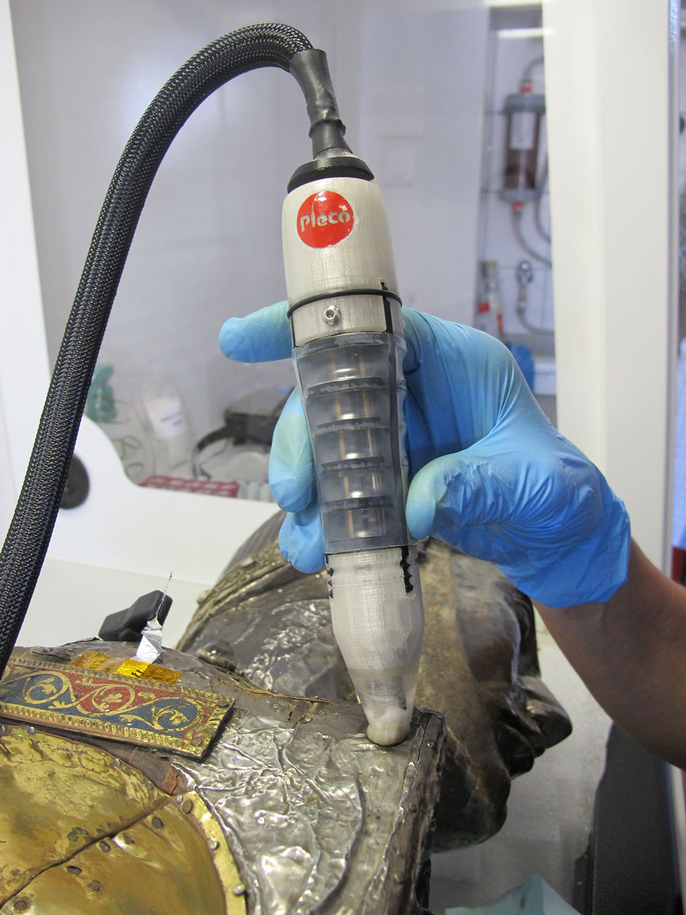
wiki/images/Le Pleco The Pleco/IMG_0143b.jpg
