fablabneuch/Pleco/wiki/images/Le Pleco The Pleco/Plomb3.jpg

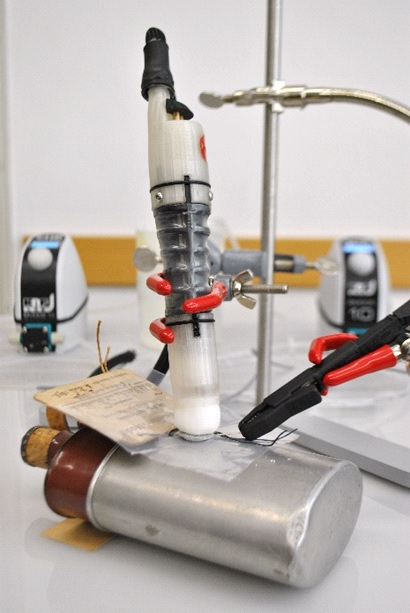
wiki/images/Le Pleco The Pleco/Plomb3.jpg
