fablabneuch/Pleco/wiki/images/Le Pleco The Pleco/united-kingdom 50.png

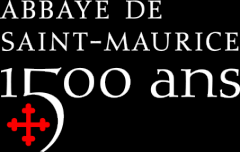
wiki/images/Le Pleco The Pleco/united-kingdom 50.png
