fablabneuch/Pleco/wiki/images/Stockage des matériaux/download (3).png

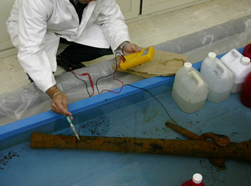
wiki/images/Stockage des matériaux/download (3).png
