fablabneuch/Pleco/wiki/images/Stockage des matériaux/download.png

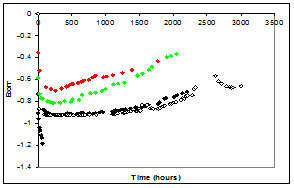
wiki/images/Stockage des matériaux/download.png
