fablabneuch/Pleco/wiki/images/Traitements de nettoyage/download (1).png

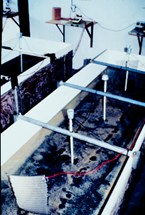
wiki/images/Traitements de nettoyage/download (1).png
