fablabneuch/Pleco/wiki/images/Traitements de nettoyage/download (2).png

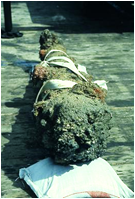
wiki/images/Traitements de nettoyage/download (2).png
