fablabneuch/Pleco/wiki/images/Traitements de nettoyage/download (3).png

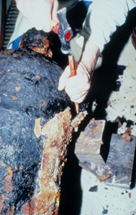
wiki/images/Traitements de nettoyage/download (3).png
