fablabneuch/Pleco/wiki/images/Traitements de nettoyage/download (4).png

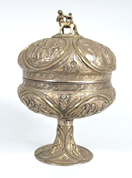
wiki/images/Traitements de nettoyage/download (4).png
