fablabneuch/Pleco/wiki/images/Traitements de nettoyage/download (5).png

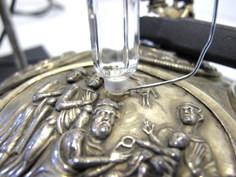
wiki/images/Traitements de nettoyage/download (5).png
