fablabneuch/Pleco/wiki/images/Traitements de nettoyage/download (6).png

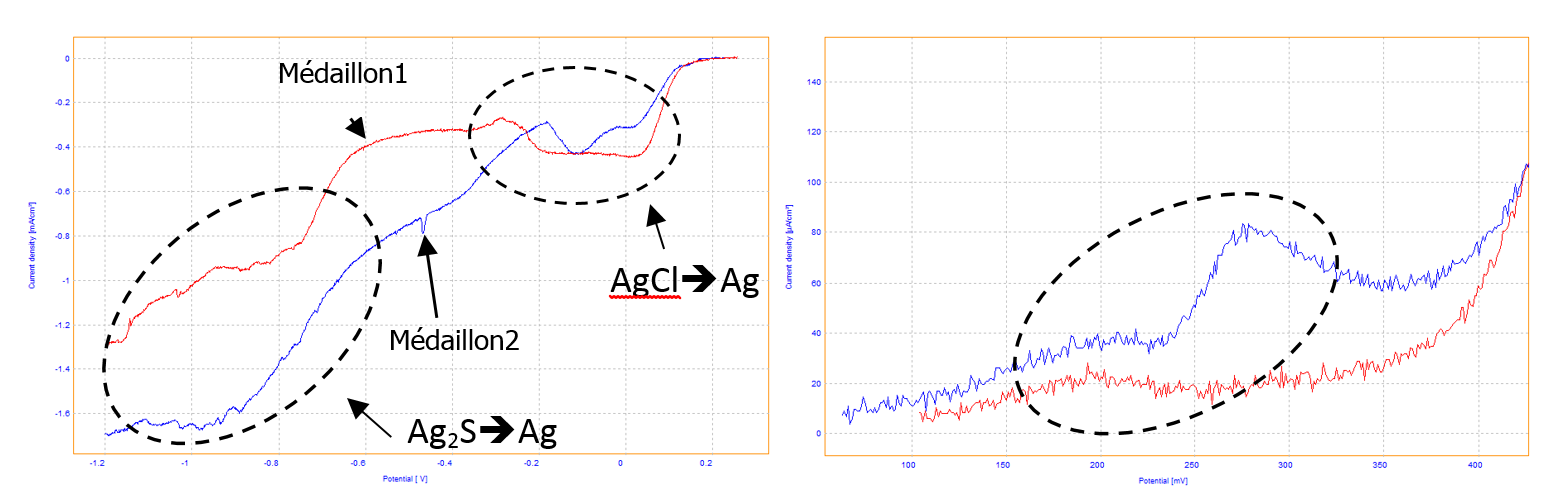
wiki/images/Traitements de nettoyage/download (6).png
