fablabneuch/Pleco/wiki/images/Traitements de nettoyage/download (7).png

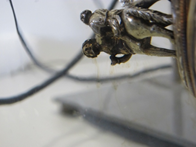
wiki/images/Traitements de nettoyage/download (7).png
