fablabneuch/Pleco/wiki/images/Traitements de nettoyage/download (8).png

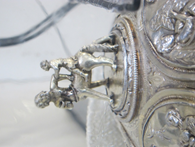
wiki/images/Traitements de nettoyage/download (8).png
