fablabneuch/Pleco/wiki/images/Traitements de nettoyage/download (9).png

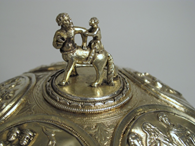
wiki/images/Traitements de nettoyage/download (9).png
