fablabneuch/Pleco/wiki/images/Traitements de nettoyage/download.png

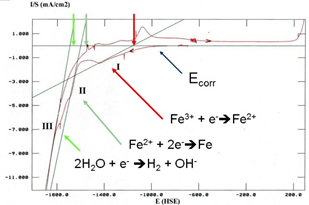
wiki/images/Traitements de nettoyage/download.png
